RHoK-Bilbao/agronautas/hardware/circuits/SD_agronautes.sch

## EAGLE design hardware/circuits/SD_agronautes.sch (2013-01-16)

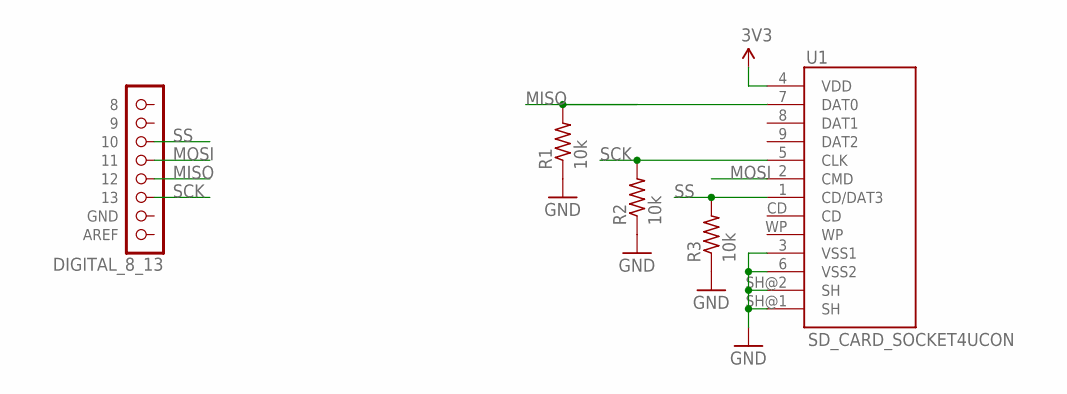
[picture p39: schematic SD_agronautes.sch]

Parts:
R1, R2, R3: 10k; 0207/10
U1: SD_CARD_SOCKET4UCON; SDCARD_4UCONN
U$2: DIGITAL_8_13; 1X08

Connections:
GND: R1.1, R2.1, R3.1, U1.3 (VSS1), U1.6 (VSS2), U1.SH@1 (SH), U1.SH@2 (SH)
MISO: R1.2, U1.7 (DAT0), U$2.4 (12)
MOSI: U1.2 (CMD), U$2.5 (11)
SCK: R2.2, U1.5 (CLK), U$2.3 (13)
SS: R3.2, U1.1 (CD/DAT3), U$2.6 (10)
VCC: U1.4 (VDD)
