RHoK-Bilbao/agronautas/hardware/circuits/interaction_agronautes.sch

## EAGLE design hardware/circuits/interaction_agronautes.sch (2013-01-16)

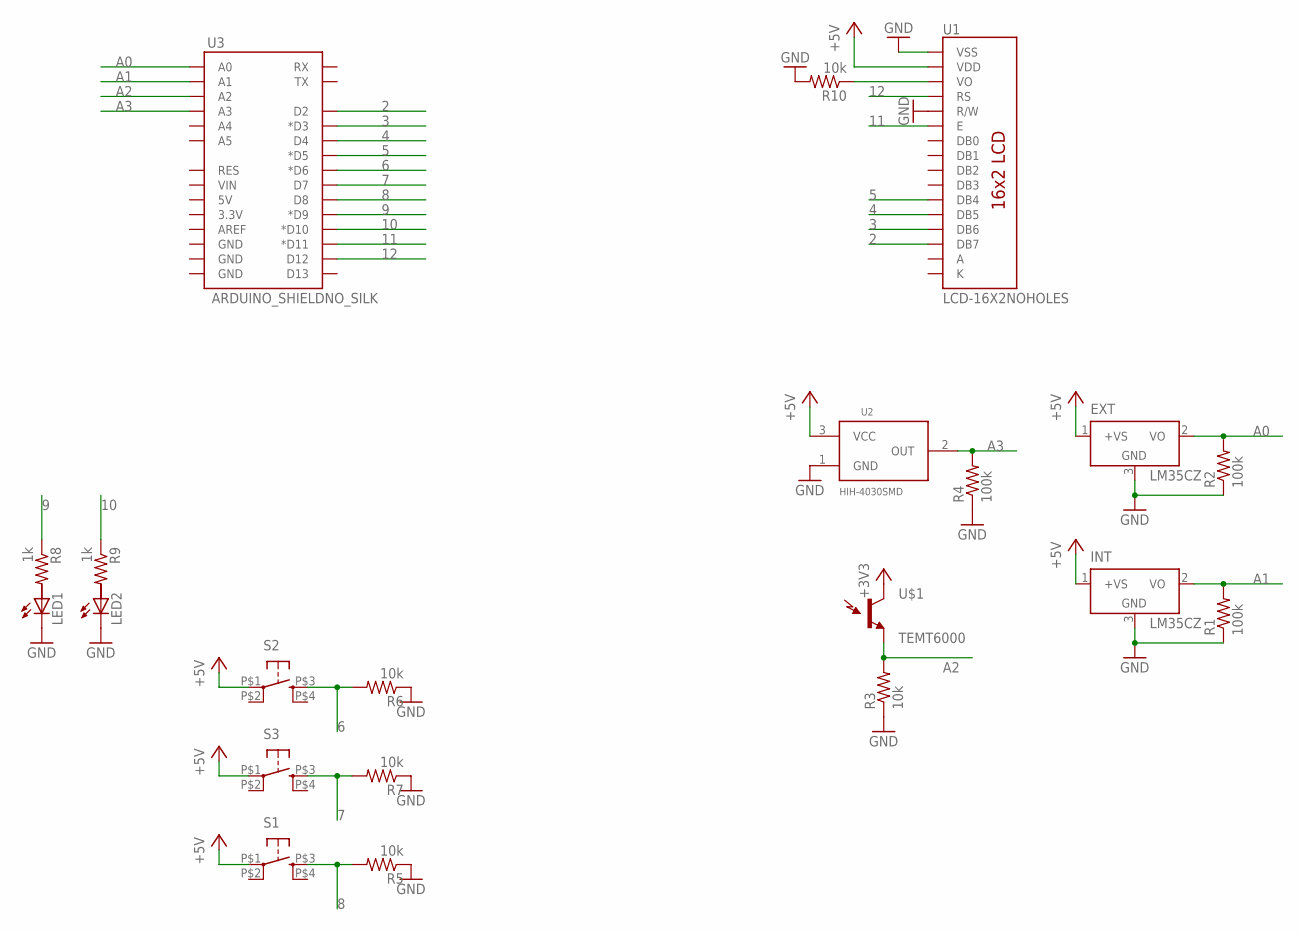
[picture p40: schematic interaction_agronautes.sch]

Parts:
EXT: LM35CZ; TO92
INT: LM35CZ; TO92
LED1, LED2: LED5MM
R1, R2, R4: 100k; 0204/7
R3, R5, R6, R7, R10: 10k; 0204/7
R8, R9: 1k; 0204/7
S1, S2, S3: TAC_SWITCHKSA_SEALED; KSA_SEALED_TAC_SWITCH
U1: LCD-16X2NOHOLES; LCD-16X2_NOHOLES
U2: HIH-4030SMD; HIH-4030
U3: ARDUINO_SHIELDNO_SILK; DUEMILANOVE_VIAS
U$1: TEMT6000; TEMT6000-SEN

Connections:
2: U1.14 (DB7), U3.D2
3: U1.13 (DB6), U3.D3 (*D3)
4: U1.12 (DB5), U3.D4
5: U1.11 (DB4), U3.D5 (*D5)
6: R6.2, S2.P$3 (3), U3.D6 (*D6)
7: R7.2, S3.P$3 (3), U3.D7
8: R5.2, S1.P$3 (3), U3.D8
9: R8.1, U3.D9 (*D9)
10: R9.1, U3.D10 (*D10)
11: U1.6 (E), U3.D11 (*D11)
12: U1.4 (RS), U3.D12
+3V3: U$1.COLLECTOR (C1)
+5V: EXT.1 (+VS), INT.1 (+VS), S1.P$1 (1), S2.P$1 (1), S3.P$1 (1), U1.2 (VDD), U2.3 (VCC)
A0: EXT.2 (VO), R2.2, U3.A0
A1: INT.2 (VO), R1.2, U3.A1
A2: R3.2, U3.A2, U$1.EMITTER (E1)
A3: R4.2, U2.2 (OUT), U3.A3
GND: EXT.3 (GND), INT.3 (GND), LED1.K (C), LED2.K (C), R1.1, R2.1, R3.1, R4.1, R5.1, R6.1, R7.1, R10.2, U1.1 (VSS), U1.5 (R/W), U2.1 (GND)
unnamed: R10.1, U1.3 (VO)
