RHoK-Bilbao/agronautas/hardware/circuits/wifi_agronautes.sch

## EAGLE design hardware/circuits/wifi_agronautes.sch (2013-01-16)

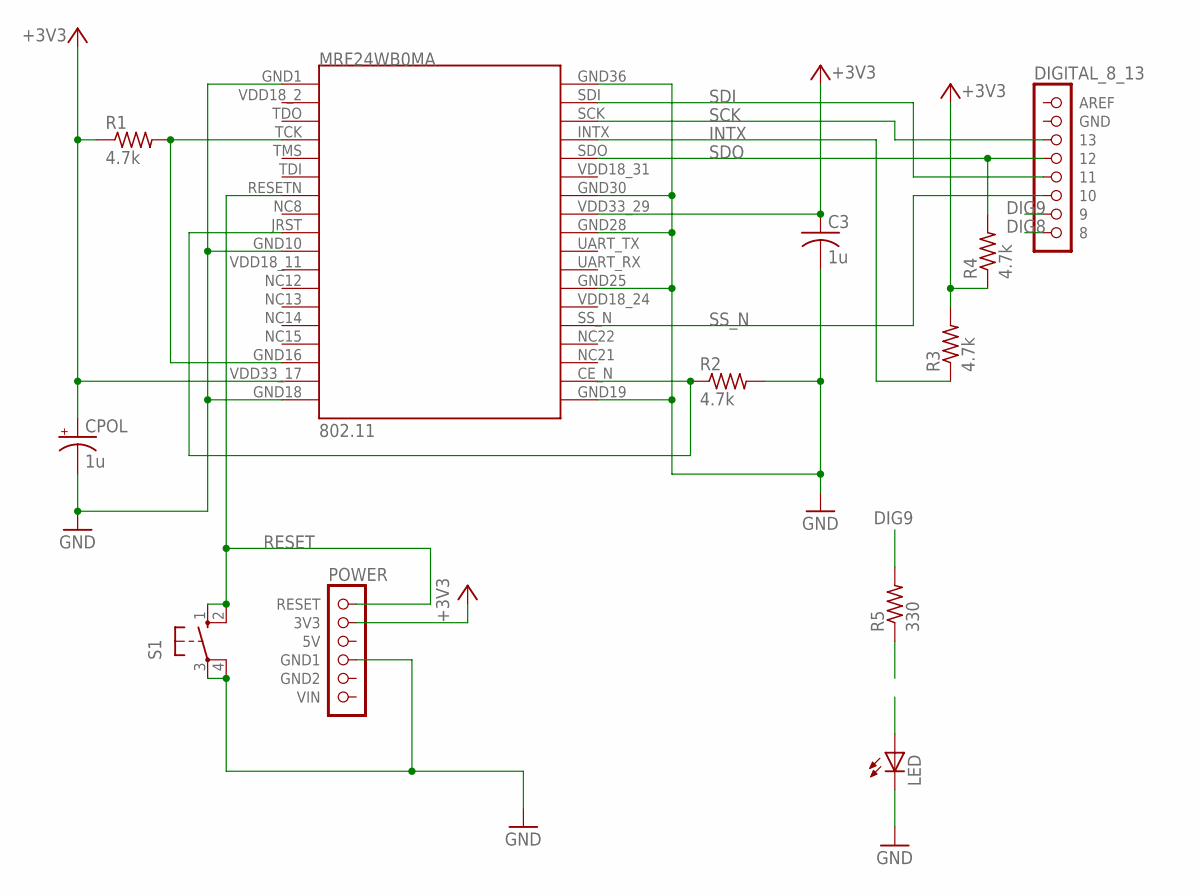
[picture p41: schematic wifi_agronautes.sch]

Parts:
C3: 1u; CAP
CPOL: 1u; PCAP
LED: LED3MM
MRF24WB0MA: 802.11; ZG2100MOD
R1, R2, R3: 4.7k; RES_SMALL
R4: 4.7k; RES
R5: 330; RES_SMALL
S1: SWITCH
U$1: POWER; 1X06
U$4: DIGITAL_8_13; 1X08

Connections:
+3V3: C3.1, CPOL.+, MRF24WB0MA.VDD33_17, MRF24WB0MA.VDD33_29, R1.1, R3.2, R4.1, U$1.2 (3V3)
DIG8: U$4.8
DIG9: R5.2, U$4.7 (9)
GND: C3.2, CPOL.-, LED.K (C), MRF24WB0MA.GND1, MRF24WB0MA.GND10, MRF24WB0MA.GND18, MRF24WB0MA.GND19, MRF24WB0MA.GND25, MRF24WB0MA.GND28, MRF24WB0MA.GND30, MRF24WB0MA.GND36, R2.2, S1.3, S1.4 (P1), U$1.4 (GND1)
GND_TIE: MRF24WB0MA.CE_N, MRF24WB0MA.JRST, R2.1
INTX: MRF24WB0MA.INTX, R3.1
RESET: MRF24WB0MA.RESETN (RSTN), S1.1 (S), S1.2 (S1), U$1.1 (RESET)
SCK: MRF24WB0MA.SCK, U$4.3 (13)
SDI: MRF24WB0MA.SDI, U$4.5 (11)
SDO: MRF24WB0MA.SDO, R4.2, U$4.4 (12)
SS_N: MRF24WB0MA.SS_N, U$4.6 (10)
VDD_TIE: MRF24WB0MA.GND16, MRF24WB0MA.TCK, R1.2
